piis3/sonos-buttons/main/sonos.h

#include <Arduino.h>
#include <HTTPClient.h>

#define HTTP_TIMEOUT 2000
#define SONOS_PORT 1400

#define ENO_CANTCONNECT 11;

int sonosOperation(int (*operation)(HTTPClient *http, IPAddress target), IPAddress targetSonos);

int volumeUp(HTTPClient *http, IPAddress targetSonos);
int volumeDown(HTTPClient *http, IPAddress targetSonos);
int sonosNext(HTTPClient *http, IPAddress targetSonos);
int sonosPlay(HTTPClient *http, IPAddress targetSonos);

IPAddress discoverSonos(std::string uid);
